bogonissATWIT/RVBP/System Block Diagram/BCM setup.PNG

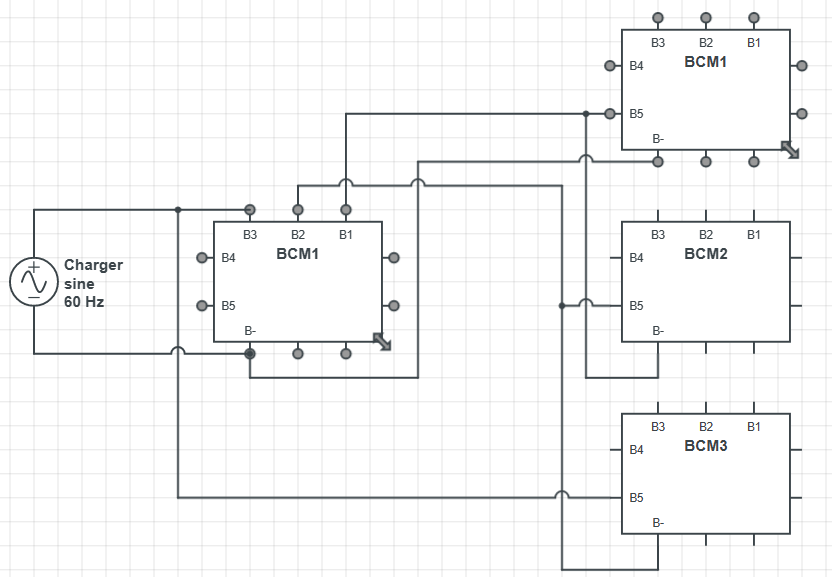
System Block Diagram/BCM setup.PNG
